ZackFreedman/Somatic/Training Utility/somatictrainer/Hands/0000.png

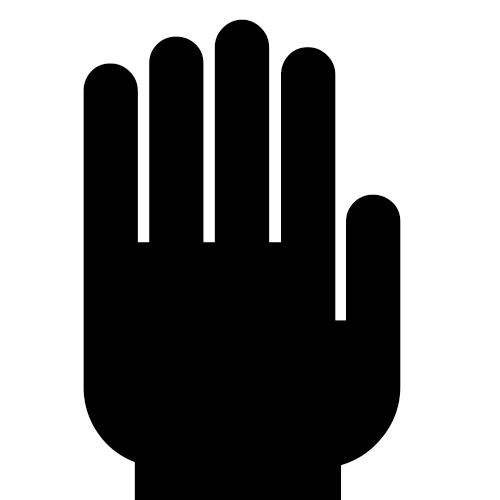
Training Utility/somatictrainer/Hands/0000.png
