ZackFreedman/Somatic/Training Utility/somatictrainer/Hands/0001.png

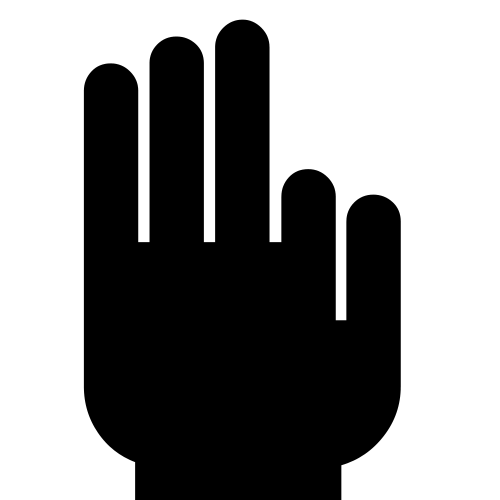
Training Utility/somatictrainer/Hands/0001.png
