ZackFreedman/Somatic/Training Utility/somatictrainer/Hands/0010.png

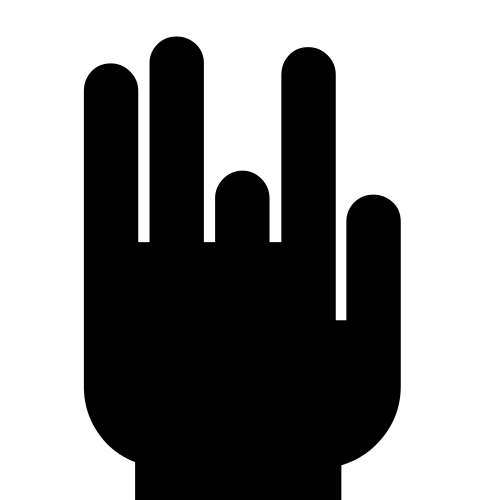
Training Utility/somatictrainer/Hands/0010.png
