ZackFreedman/Somatic/Training Utility/somatictrainer/Hands/0011.png

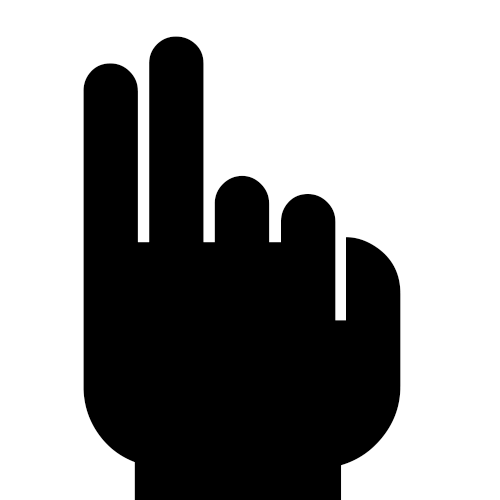
Training Utility/somatictrainer/Hands/0011.png
