ZackFreedman/Somatic/Training Utility/somatictrainer/Hands/0111.png

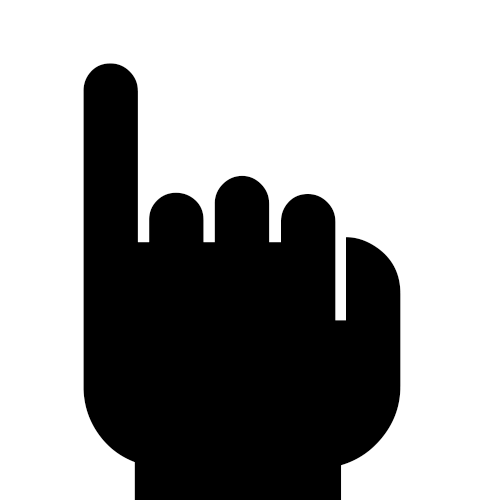
Training Utility/somatictrainer/Hands/0111.png
