ZackFreedman/Somatic/Training Utility/somatictrainer/Hands/1001.png

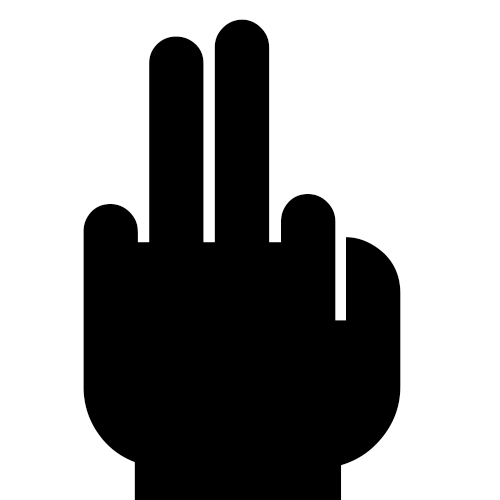
Training Utility/somatictrainer/Hands/1001.png
