ZackFreedman/Somatic/Electronics/Prototype Schematic.sch

## EAGLE design Electronics/Prototype Schematic.sch (2020-10-27)

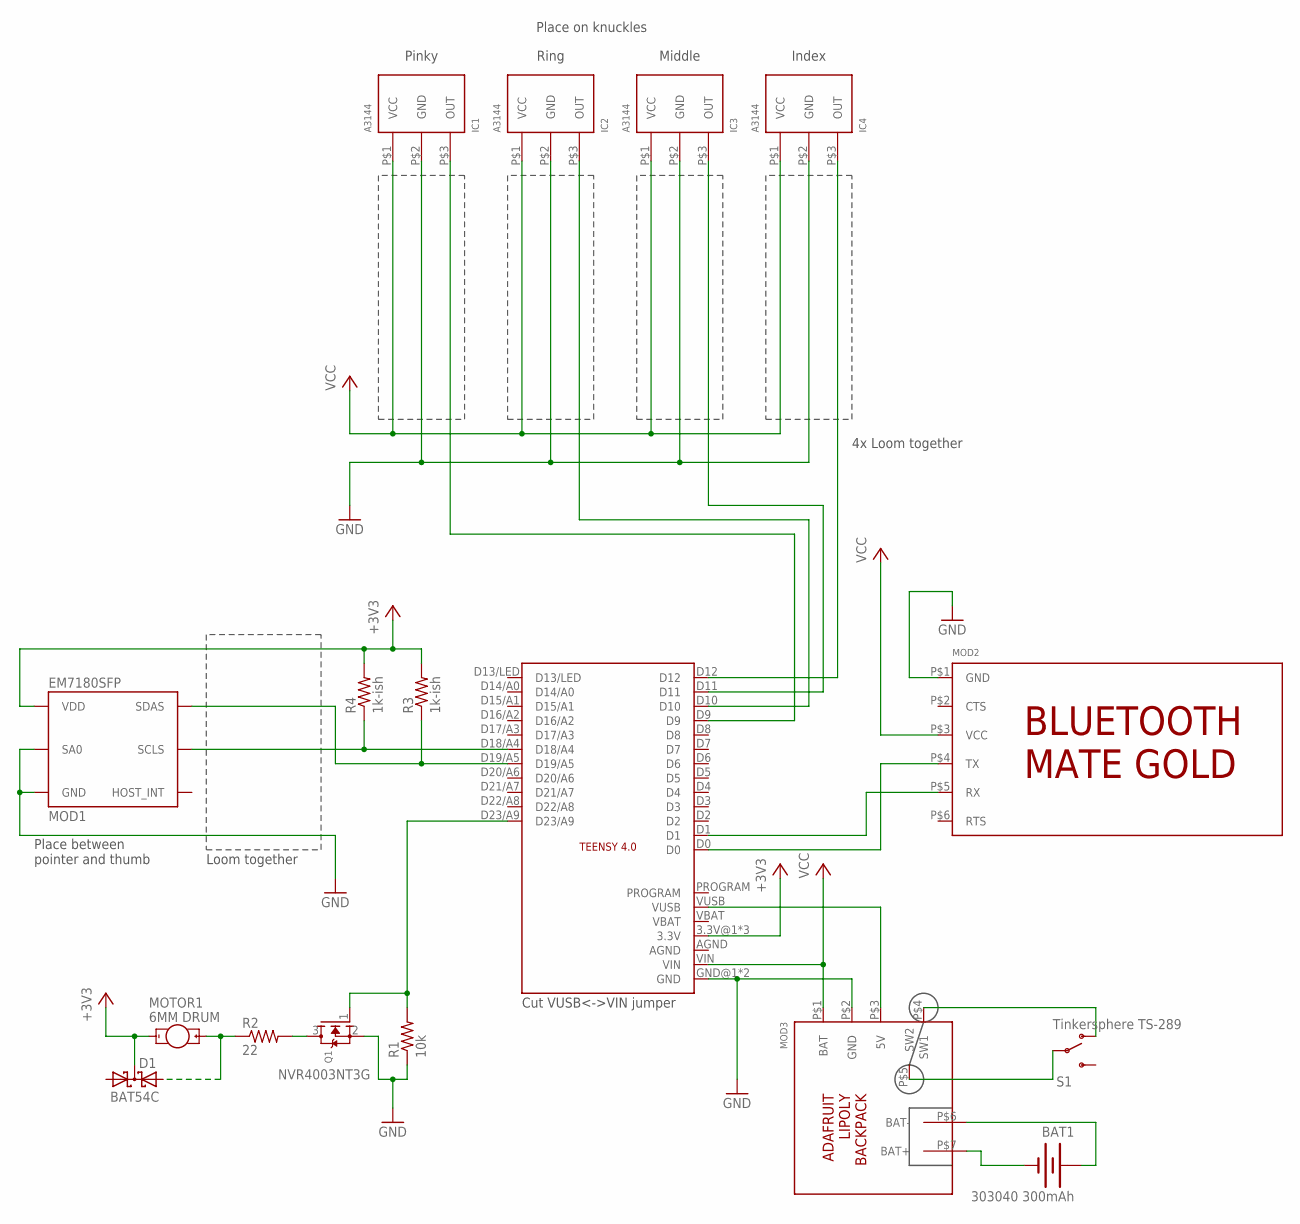
[picture p22: schematic Prototype Schematic.sch]

Parts:
BAT1: 303040 300mAh; LIPO-110-TABS
D1: BAT54C; SOT23
IC1, IC2, IC3, IC4: A3144; DUMMY-PIN
MOD1: EM7180SFP
MOD2: BLUETOOTH-MATE-GOLD; DUMMY-PIN
MOD3: LIPOLY-BACKPACK; DUMMY-PIN
MOTOR1: 6MM DRUM; VIBE-MOTOR-10MM
Q1: MOSFET-NREFLOW; SOT23
R1: 10k; R0603
R2: 22; R0603
R3, R4: 1k-ish; R0603
S1: Tinkersphere TS-289; SWITCH-SPDT
U$1: TEENSY4.0

Connections:
+3V3: D1.3 (CC), MOD1.P$1 (VDD), MOTOR1.-, R3.2, R4.2, U$1.3.3V@1 (3.3V)
GND: IC1.P$2 (GND), IC2.P$2 (GND), IC3.P$2 (GND), IC4.P$2 (GND), MOD1.P$5 (SA0), MOD1.P$6 (GND), MOD2.P$1 (GND), MOD3.P$2 (GND), Q1.2 (S), R1.1, U$1.GND@1 (GND)
unnamed: MOD1.P$3 (SCLS), R4.1, U$1.D18/A4
unnamed: MOD1.P$2 (SDAS), R3.1, U$1.D19/A5
unnamed: Q1.1 (G), R1.2, U$1.D23/A9
unnamed: D1.2 (A2), MOTOR1.+, R2.1
unnamed: Q1.3 (D), R2.2
unnamed: MOD3.P$5 (SW2), S1.2
unnamed: MOD3.P$4 (SW1), S1.1 (O)
unnamed: BAT1.-, MOD3.P$7 (BAT+)
unnamed: BAT1.+, MOD3.P$6 (BAT-)
unnamed: MOD2.P$4 (TX), U$1.D0
unnamed: MOD2.P$5 (RX), U$1.D1
unnamed: MOD3.P$3 (5V), U$1.VUSB
unnamed: IC4.P$3 (OUT), U$1.D12
unnamed: IC3.P$3 (OUT), U$1.D11
unnamed: IC2.P$3 (OUT), U$1.D10
unnamed: IC1.P$3 (OUT), U$1.D9
VCC: IC1.P$1 (VCC), IC2.P$1 (VCC), IC3.P$1 (VCC), IC4.P$1 (VCC), MOD2.P$3 (VCC), MOD3.P$1 (BAT), U$1.VIN

Notes on the sheet:
Loom together
Cut VUSB<->VIN jumper
Pinky
Ring
Middle
Index
4x Loom together
Place between pointer and thumb
Place on knuckles
NVR4003NT3G
